lazerduck/fuse-vault/v1/docs/security-design.md

# Fuse Vault security and provisioning design

Review update (2026-09-14): the [storage and responsiveness redesign](storage-performance-redesign.md)
retains Ascon and selectable encryption while proposing a new data layout and
measured password-hardening budget. Existing recovery and KDF descriptions below
describe the prototype; the redesign remains a review draft, not implemented code.

Status: architectural baseline for development. Cryptographic profile details
remain provisional until they have test vectors, measurements on RP2354A, and
independent review.

## Security objective

Fuse Vault provides encrypted storage at rest and deliberate, selective
disclosure after local user authentication. The host never receives the vault
unlock secret, device secret, volume master key, or derived storage keys. A
host can access plaintext that the user deliberately exposes while the relevant
USB mode is active; the device cannot protect that plaintext from a malicious
host after disclosure.

The design does not depend on a single cryptographic family. During V1 setup the
user selects an ordered stack from algorithms compiled into the reviewed
firmware registry. Vault-header format V2 authenticates one to four permanent
algorithm IDs and versions. This is not arbitrary user-supplied code: unknown or
unavailable algorithms fail locked and are never silently replaced.

## Key hierarchy

The following values have distinct roles:

- **Entry encoding:** canonical, versioned bytes generated by the selected
  human-input method. It is not a cryptographic key.
- **Input key:** a 32-byte result from a password-hardening function using the
  entry encoding, a random per-vault salt, and stored parameters.
- **Device roots:** two independently generated random 32-byte values unique
  to the physical device. Neither is ever stored on the SD card. The roots are
  assigned permanently to the SHA-256 and Keccak families and are never used
  directly as operational keys.
- **Key-encryption keys:** independent values derived from the input key and
  corresponding device root by the profile's two cryptographic families.
- **Volume master key (VMK):** a random 32-byte value generated during setup.
  It is wrapped by both profile branches and is never derived directly from
  human input.
- **Layer keys:** keys derived from the VMK with unique labels containing the
  profile version, algorithm identifier, direction/purpose, and vault ID.

Changing an entry method or secret rewraps the random VMK after successful
authentication; it does not require re-encrypting every data block.

The implemented selectable data layers are AES-256-XTS and ChaCha20. Their
ordered transforms sit inside the mandatory Ascon-AEAD128 storage record, which
provides authenticated addressing, metadata integrity, and torn-write recovery.
SM4-XTS has a reserved identifier but is unavailable rather than a no-op.

## Default dual-family profile

The implemented provisional V1 profile uses two independently designed
derivation and wrapping branches, both of which are required to unlock the
VMK:

1. PBKDF2-HMAC-SHA-256 hardens the canonical entry with a random salt and a
   recorded iteration count. HMAC-SHA-256 then combines that result with device
   Root A to derive an AES-256-GCM key. AES-256-GCM forms the inner envelope.
2. A versioned iterated-KMAC256 construction hardens the same canonical entry
   under an independent salt, iteration count, and encoding. KMAC256 combines
   that result with Root B to derive a 128-bit Ascon key. NIST Ascon-AEAD128
   authenticates the complete inner envelope as the outer layer.

The fixed envelope is 92 bytes: a 16-byte Ascon nonce, a 60-byte encrypted
inner envelope, and a 16-byte Ascon tag. The inner envelope contains a 12-byte
AES nonce, 32-byte encrypted VMK, and 16-byte AES-GCM tag. Both AEAD layers use
the same canonical associated data containing the envelope version, header
sequence, profile ID, entry-method ID, vault ID, both salts, both costs, and
wrapped length. A wrong entry, either wrong device root, or alteration of any
authenticated metadata therefore prevents VMK recovery.

PBKDF2 was selected for the first implementation instead of committing to
scrypt parameters before RP2354A SRAM use and latency can be measured. The
device-held roots and rollback-resistant ten-attempt limit prevent an SD-card
image from becoming a standalone password oracle, but the final iteration
counts and whether the SHA branch moves to scrypt remain review items. Header
costs are bounded to prevent malicious metadata from causing unbounded work.

Every cryptographic operation has a fixed ASCII domain label beginning with
`fuse-vault/v1/`. All variable-length inputs use length-prefix encoding. The
profile ID and all parameters required to reproduce derivation are
authenticated metadata.

The primary references are [NIST SP 800-132 for
PBKDF2](https://csrc.nist.gov/pubs/sp/800/132/final), [NIST SP 800-185 for
KMAC](https://csrc.nist.gov/pubs/sp/800/185/final), [NIST SP 800-38D for
GCM](https://csrc.nist.gov/pubs/sp/800/38/d/final), and [NIST SP 800-232 for
Ascon](https://csrc.nist.gov/pubs/sp/800/232/final). Reference documents do not
by themselves constitute a review of the composed Fuse Vault profile.

## Vault header

The removable card contains redundant authenticated copies of a versioned
header. At minimum it records:

- format version and header sequence number;
- random vault ID;
- crypto profile ID;
- entry-method ID and encoding version;
- salts and KDF parameters for both branches;
- ordered data-encryption layer identifiers and parameters;
- the twice-wrapped VMK and its authentication data;
- encrypted filesystem geometry and integrity-tree roots where applicable.

The header contains no device secret and no independent verifier of the human
secret. Correct authentication is established only by successfully validating
both wrapping layers and the authenticated header.

## First-time setup

An unprovisioned device exposes no USB data interface. The setup sequence is:

1. Explain that no vault exists and require an explicit start action.
2. Run hardware and entropy-source checks.
3. Select an entry method and its versioned configuration.
4. Enter the secret twice and compare canonical encodings.
5. Confirm the ten-attempt destructive-lockout and no-recovery policy.
6. Generate the device secret, vault ID, salts, and VMK from the approved random
   source.
7. Calibrate or select the fixed, recorded profile parameters.
8. Derive both wrapping keys and wrap the VMK through both profile branches.
9. Initialise the encrypted card and redundant authenticated headers.
10. Persist rollback-resistant attempt state at zero.
11. Erase transient inputs and derived keys from RAM.
12. Require a complete verification unlock before marking setup complete.

The implemented `device_provisioning.c` transaction covers the device-root and
initial-journal portion of this sequence. Its critical commit order is journal
erase, authenticated initial-record write, journal verification, OTP root
write, OTP active-marker write, root read-back, and a second journal
verification using the read-back roots. It is intentionally not connected to
the setup-success event until the KDF, wrapped VMK, and vault-header stages can
run before the OTP active marker.

OTP and permanent secure-boot settings are not changed by ordinary development
firmware. Production OTP provisioning is a separate, deliberately invoked
process with read-back verification before irreversible lock bits are set.
The proposed device-secret lifecycle and RP2354A storage mapping are detailed in
[rp2354-storage.md](rp2354-storage.md).

## Attempt accounting

An attempt must be durably reserved before an entered secret is checked. This
prevents power removal during authentication from providing unlimited free
guesses. Successful authentication resets the counter only after both wrapping
layers and the authenticated header validate.

The application state machine enforces this ordering by entering an
attempt-reservation state and emitting only a persistent-counter command. It
cannot emit the authentication command until the platform acknowledges that
write. The host development backend implements this with two alternating,
sequence-numbered records and atomic file replacement; its CRC is only for
corruption recovery and is not the production counter-authentication design.

The portable production journal core uses two flash sectors, append-only
256-byte records, sequence linkage, vault binding, and two independent
authentication tags. Recovery ignores torn or unauthenticated records and
sector rotation retains the latest valid record before erasing old history.
The implemented authenticator derives one journal key from Root A using
SP 800-108 counter mode with HMAC-SHA-256 and another from Root B using the
SP 800-108 KMAC256 construction. Full 32-byte HMAC-SHA-256 and KMAC256 tags are
required. Labels and device context separate these keys from every other use.
Host known-answer tests cover the HMAC derivation/tag path and the official
NIST KMAC256 sample. The journal fault-injection tests retain a deliberately
non-cryptographic authenticator so every write boundary can be controlled.

The counter cannot rely solely on the removable card because an attacker could
restore an older card image. Internal-flash journalling prevents ordinary SD
rollback and handles interrupted writes, but an invasive attacker who can clone
and restore the RP2354A's internal flash remains outside this V1 mechanism. The
hardware flash adapter, endurance budget, dual-family MAC implementation, and
behaviour at the tenth reserved attempt remain required before destructive
lockout is enabled on hardware.

## Secret lifecycle

Entry state, canonical encodings, KDF work areas, wrapping keys, the VMK, and
layer keys are separate buffers with explicit owners and lifetimes. Sensitive
buffers are erased on cancellation, failure, mode exit, USB disconnect, and
fault entry. Compiler-resistant erasure and tests of those transitions are
required. The host simulator never implements a plaintext storage fallback.

## Decisions still requiring review

- Final parameters and measured latency for both password-hardening branches,
  including whether scrypt fits the SHA branch on the production board.
- Independent review of the two-family credential-envelope composition.
- Authenticated-encryption algorithms for storage sectors.
- Nonce construction and power-loss-safe authenticated metadata updates.
- Rollback-resistant attempt accounting within flash/OTP endurance limits.
- Secure boot, debug lockdown, firmware update, and recovery policy.
- Side-channel behaviour and constant-time implementation of secret operations.
