lazerduck/fuse-vault/CaseDesign/drill_schedule.csv

x | y | end_x | end_y | diameter | kind | plating | sources
62.52489 | -16.93189 | 62.52489 | -16.93189 | 0.95001 | round | NPTH | Drill_NPTH_Through.DRL:17
58.12511 | -16.93189 | 58.12511 | -16.93189 | 0.95001 | round | NPTH | Drill_NPTH_Through.DRL:18
71.025 | -8.79907 | 71.025 | -8.79907 | 1.0 | round | NPTH | Drill_NPTH_Through.DRL:20
71.025 | -13.29919 | 71.025 | -13.29919 | 1.0 | round | NPTH | Drill_NPTH_Through.DRL:21
52.45405 | -4.07899 | 52.45405 | -4.07899 | 1.2 | round | NPTH | Drill_NPTH_Through.DRL:23
60.45403 | -4.07899 | 60.45403 | -4.07899 | 1.2 | round | NPTH | Drill_NPTH_Through.DRL:24
31.8135 | -1.0795 | 31.8135 | -1.0795 | 0.305 | round | PTH | Drill_PTH_Through.DRL:21;Drill_PTH_Through_Via.DRL:15
31.877 | -2.286 | 31.877 | -2.286 | 0.305 | round | PTH | Drill_PTH_Through.DRL:22;Drill_PTH_Through_Via.DRL:16
42.57501 | -12.51718 | 42.57501 | -12.51718 | 0.305 | round | PTH | Drill_PTH_Through.DRL:24;Drill_PTH_Through_Via.DRL:18
45.07771 | -5.79899 | 45.07771 | -5.79899 | 0.305 | round | PTH | Drill_PTH_Through.DRL:25;Drill_PTH_Through_Via.DRL:19
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
