lazerduck/fuse-vault/CaseDesign/prototype-e/base.step

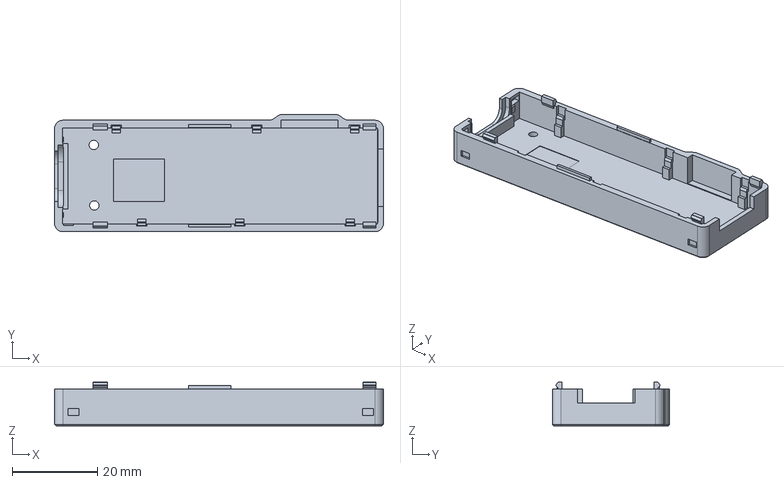
[picture p19: CAD file, 2026-10-05]
CaseDesign/prototype-e/base.step
77.3 x 27.6 x 10.3 mm
