lazerduck/fuse-vault/CaseDesign/prototype-e/lid_snap_light.step

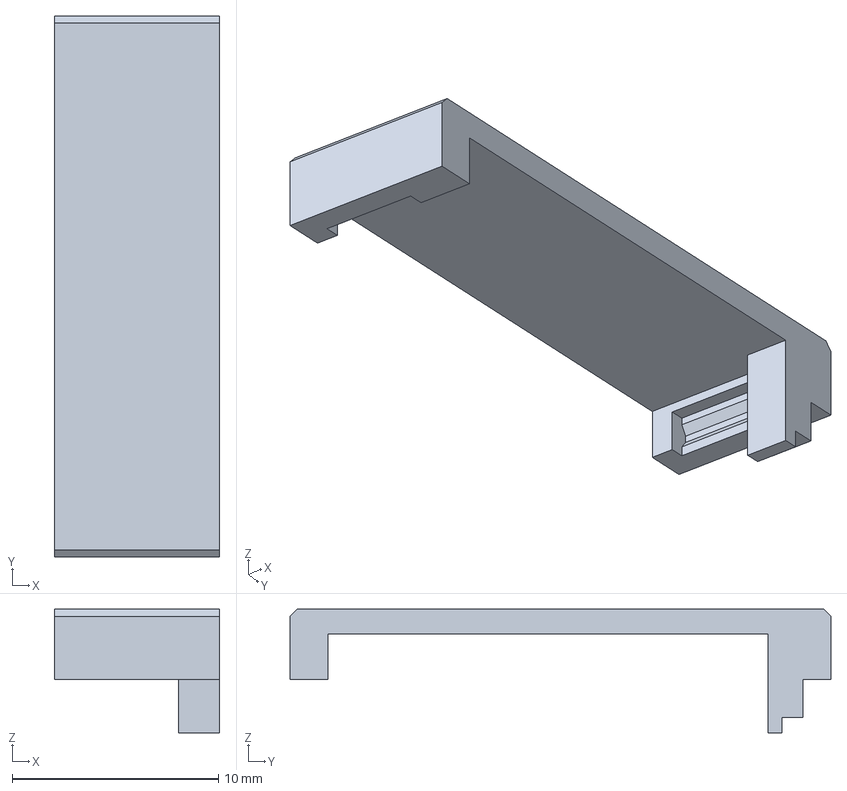
[picture p20: CAD file, 2026-10-05]
CaseDesign/prototype-e/lid_snap_light.step
8.00 x 26.2 x 6.00 mm
