lazerduck/fuse-vault/results/ui-polish-20260921.png

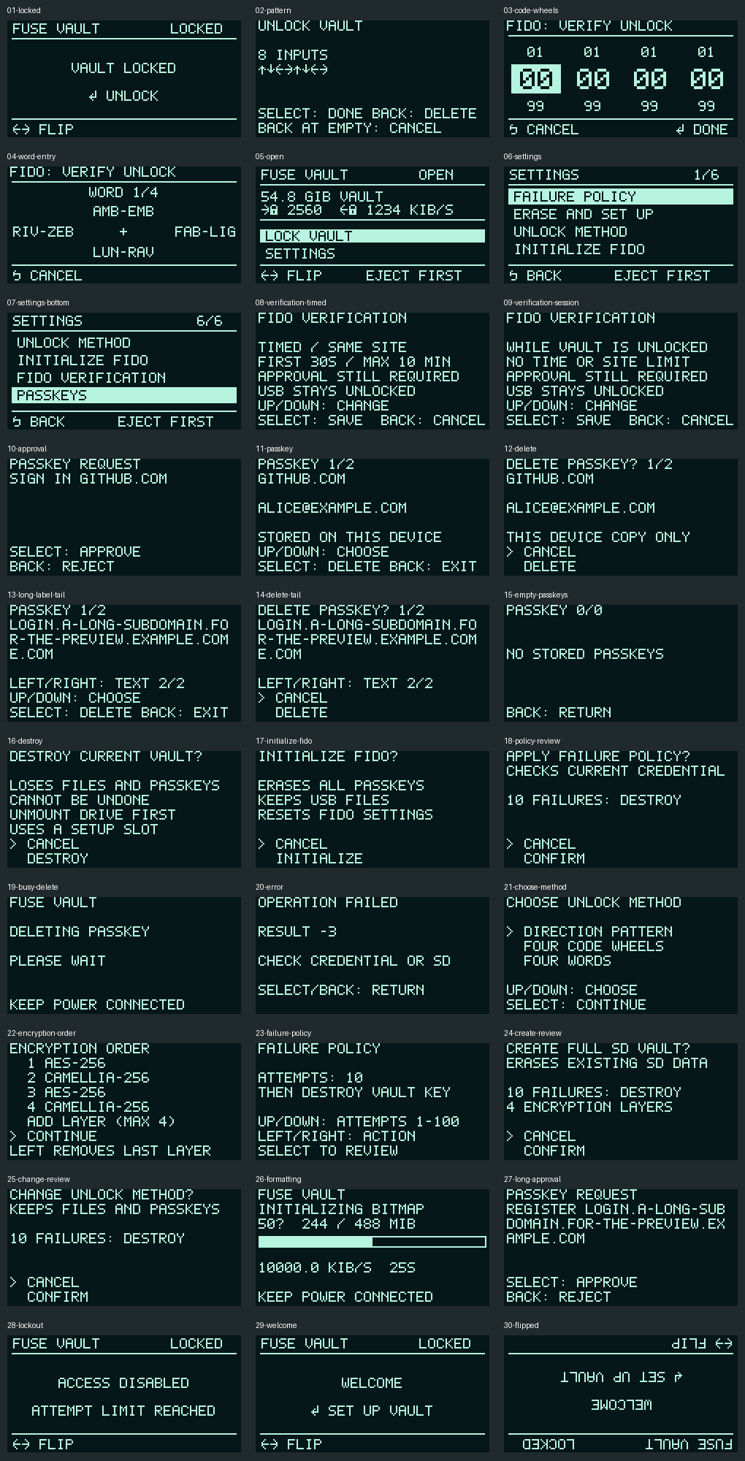
results/ui-polish-20260921.png
