lazerduck/fuse-vault/results/ui-polish-20261001/dashboard.png

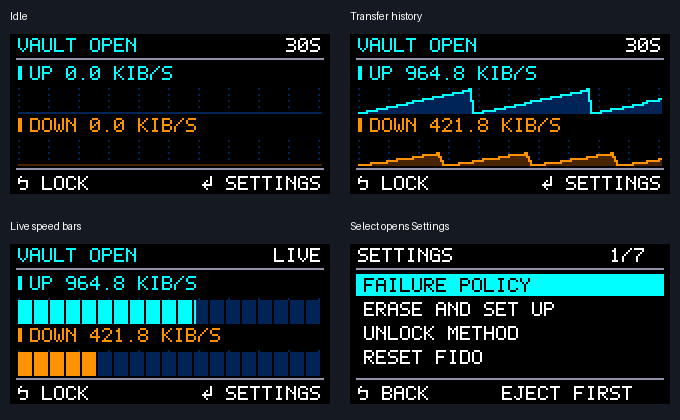
results/ui-polish-20261001/dashboard.png
