lazerduck/fuse-vault/results/ui-polish-20261001/refinements.png

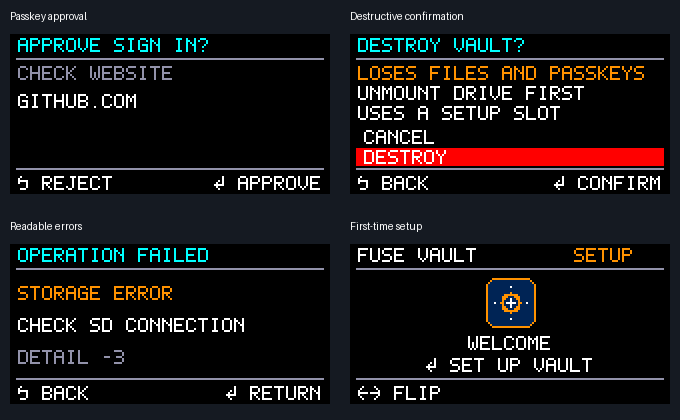
results/ui-polish-20261001/refinements.png
