lazerduck/fuse-vault/results/ui-polish-20261001/screens.png

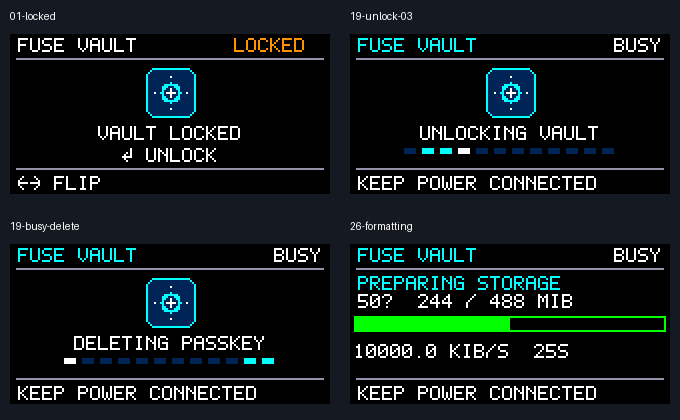
results/ui-polish-20261001/screens.png
