lazerduck/fuse-vault/results/ui-polish-20261001/unlock.gif

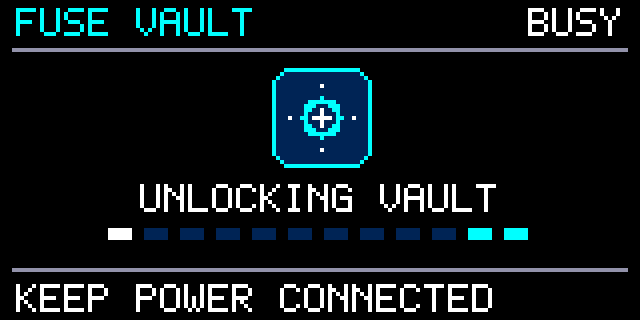
results/ui-polish-20261001/unlock.gif
