lazerduck/fuse-vault/results/ui-style-20260921.png

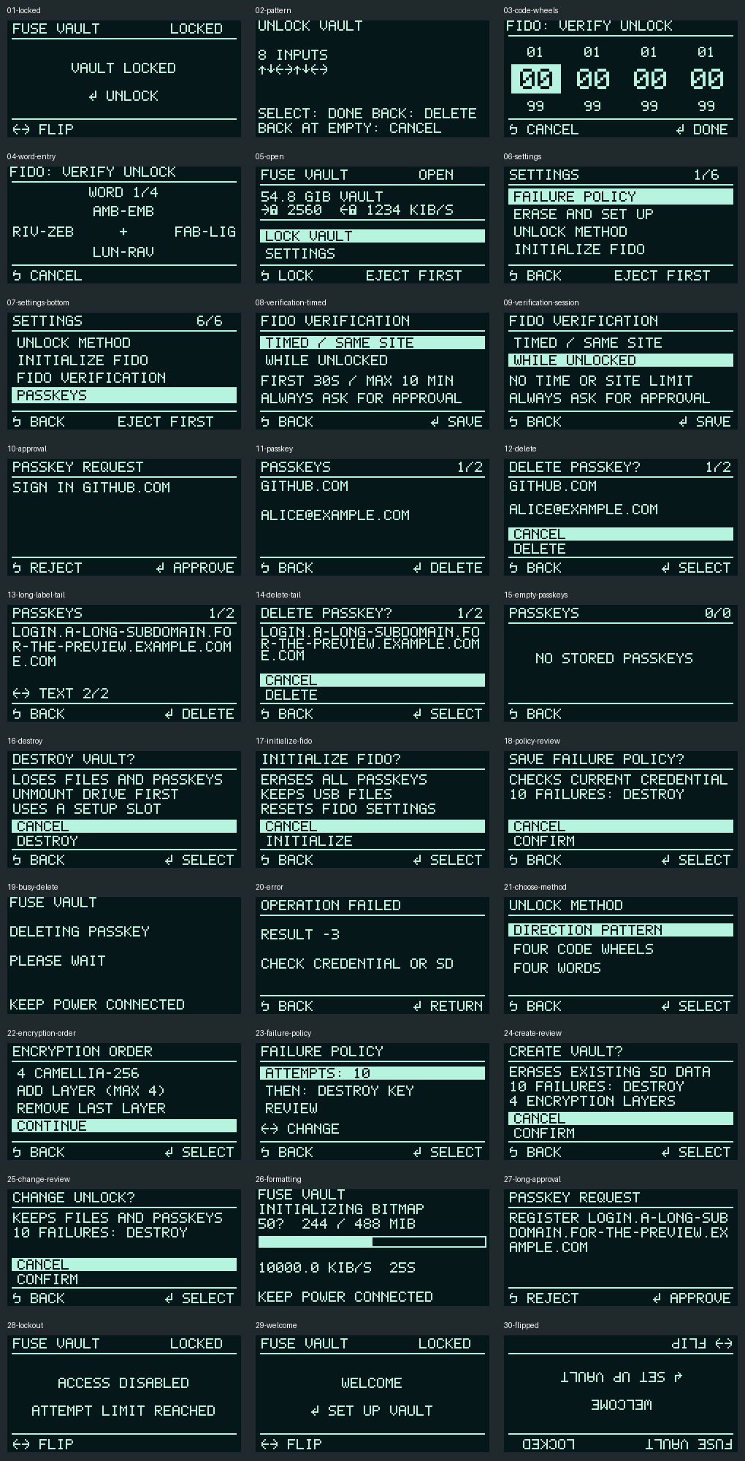
results/ui-style-20260921.png
