lazerduck/fuse-vault/v1/firmware/include/fuse_vault/app.h

#ifndef FUSE_VAULT_APP_H
#define FUSE_VAULT_APP_H

#include "fuse_vault/entry_method.h"
#include "fuse_vault/passkeys.h"
#include "fuse_vault/persistence.h"

#include <stdbool.h>
#include <stdint.h>

#define FV_MAX_UNLOCK_ATTEMPTS 10u
#define FV_UI_LINE_COUNT 4u
#define FV_UI_TEXT_CAPACITY 32u
#define FV_SECRET_WHEEL_COUNT 3u
#define FV_SECRET_WHEEL_VALUES 100u
#define FV_SECRET_DIRECTION_MAX 16u
#define FV_SECRET_KEYPAD_MAX 12u
#define FV_SECRET_WORD_COUNT 4u
#define FV_SECRET_WORD_EMPTY UINT8_MAX

typedef enum {
    FV_STATE_BOOTING = 0,
    FV_STATE_BOOT_MEDIA_REQUIRED,
    FV_STATE_SETUP_REQUIRED,
    FV_STATE_SETUP_MEDIA_CHECKING,
    FV_STATE_SETUP_MEDIA_CONFIRM,
    FV_STATE_SETUP_MEDIA_INITIALIZING,
    FV_STATE_SETUP_MEDIA_ERROR,
    FV_STATE_SETUP_METHOD_SELECT,
    FV_STATE_SETUP_SECRET_ENTRY,
    FV_STATE_SETUP_SECRET_CONFIRM,
    FV_STATE_SETUP_SECRET_MISMATCH,
    FV_STATE_SETUP_STACK_SELECT,
    FV_STATE_SETUP_POLICY_CONFIRM,
    FV_STATE_PROVISIONING,
    FV_STATE_MODE_SELECT,
    FV_STATE_VAULT_SECRET_ENTRY,
    FV_STATE_VAULT_RESERVING_ATTEMPT,
    FV_STATE_VAULT_AUTHENTICATING,
    FV_STATE_VAULT_RECORDING_SUCCESS,
    FV_STATE_VAULT_UNLOCKED,
    FV_STATE_FIDO_READY,
    FV_STATE_PASSKEY_LIST,
    FV_STATE_PASSKEY_DELETE_CONFIRM,
    FV_STATE_SETTINGS,
    FV_STATE_CHANGE_METHOD,
    FV_STATE_CHANGE_SECRET,
    FV_STATE_CHANGE_CONFIRM,
    FV_STATE_CHANGE_MISMATCH,
    FV_STATE_CHANGE_REVIEW,
    FV_STATE_CHANGE_SAVING,
    FV_STATE_CHANGE_SAVED,
    FV_STATE_DESTROYED,
    FV_STATE_FAULT,
} fv_state_t;

typedef enum {
    FV_MODE_VAULT = 0,
    FV_MODE_FIDO,
    FV_MODE_SETTINGS,
    FV_MODE_COUNT,
} fv_mode_t;

typedef enum {
    FV_EVENT_BOOT_COMPLETED = 0,
    FV_EVENT_BOOT_MEDIA_REQUIRED,
    FV_EVENT_UP,
    FV_EVENT_DOWN,
    FV_EVENT_LEFT,
    FV_EVENT_RIGHT,
    FV_EVENT_SELECT,
    FV_EVENT_BACK,
    FV_EVENT_AUTH_SUCCEEDED,
    FV_EVENT_AUTH_FAILED,
    FV_EVENT_ATTEMPT_COUNTER_STORED,
    FV_EVENT_PROVISIONING_SUCCEEDED,
    FV_EVENT_PROVISIONING_FAILED,
    FV_EVENT_MEDIA_FOUND,
    FV_EVENT_MEDIA_PREPARED,
    FV_EVENT_MEDIA_FAILED,
    FV_EVENT_LOCK_REQUESTED,
    FV_EVENT_USB_EJECTED,
    FV_EVENT_STORAGE_FAILED,
    FV_EVENT_CREDENTIAL_CHANGED,
    FV_EVENT_FATAL_ERROR,
} fv_event_t;

typedef enum {
    FV_COMMAND_NONE = 0,
    FV_COMMAND_BEGIN_PROVISIONING = 1u << 0,
    FV_COMMAND_BEGIN_AUTHENTICATION = 1u << 1,
    FV_COMMAND_USB_ATTACH_MSC = 1u << 2,
    FV_COMMAND_USB_ATTACH_FIDO = 1u << 3,
    FV_COMMAND_USB_DETACH = 1u << 4,
    FV_COMMAND_ERASE_TRANSIENT_SECRET = 1u << 5,
    FV_COMMAND_ERASE_SESSION_KEYS = 1u << 6,
    FV_COMMAND_DESTROY_DEVICE_SECRET = 1u << 7,
    FV_COMMAND_STORE_ATTEMPT_COUNTER = 1u << 8,
    FV_COMMAND_INSPECT_MEDIA = 1u << 9,
    FV_COMMAND_PREPARE_MEDIA = 1u << 10,
    FV_COMMAND_PASSKEY_BEGIN = 1u << 11,
    FV_COMMAND_PASSKEY_READ = 1u << 12,
    FV_COMMAND_PASSKEY_DELETE = 1u << 13,
    FV_COMMAND_PASSKEY_END = 1u << 14,
    FV_COMMAND_CHANGE_CREDENTIAL = 1u << 15,
} fv_command_t;

typedef uint32_t fv_command_set_t;

typedef struct {
    uint8_t values[FV_SECRET_WHEEL_COUNT];
    uint8_t selected;
} fv_wheel_entry_t;

typedef struct {
    uint8_t values[FV_SECRET_DIRECTION_MAX];
    uint8_t length;
} fv_direction_entry_t;

typedef struct {
    uint8_t digits[FV_SECRET_KEYPAD_MAX];
    uint8_t length;
    uint8_t selected;
} fv_keypad_entry_t;

typedef struct {
    uint8_t words[FV_SECRET_WORD_COUNT];
    uint8_t selected;
    uint8_t depth; /* Number of four-way groups chosen: 0, 1, or 2. */
    uint8_t prefix;
    bool reviewing;
} fv_word_entry_t;

typedef struct {
    fv_entry_method_t method;
    union {
        fv_wheel_entry_t wheels;
        fv_direction_entry_t directions;
        fv_keypad_entry_t keypad;
        fv_word_entry_t word_list;
    } state;
} fv_secret_entry_t;

typedef struct {
    fv_state_t state;
    fv_mode_t selected_mode;
    fv_entry_method_t selected_entry_method;
    fv_secret_entry_t secret_entry;
    fv_secret_entry_t setup_secret_entry;
    /* Settings draft never replaces the active method until durable commit. */
    fv_secret_entry_t change_secret_entry;
    fv_entry_method_t change_entry_method;
    uint8_t selected_setting;
    fv_encryption_stack_descriptor_t selected_encryption_stack;
    uint8_t selected_stack_preset;
    uint8_t failed_attempts;
    bool provisioned;
    bool fido_available;
    bool session_unlocked;
    bool fido_waiting;
    bool fido_reset_pending;
    fv_passkey_t passkey;
    uint16_t passkey_index, passkey_count, passkey_offset;
} fv_app_t;

typedef struct {
    bool secret_controls;
    bool hide_controls;
    bool direction_icons;
    bool word_picker;
    char word_choices[4][12]; /* Up, Right, Down, Left. */
    bool select_enabled;
    char back_action[8];
    char select_action[8];
    char title[FV_UI_TEXT_CAPACITY];
    char lines[FV_UI_LINE_COUNT][FV_UI_TEXT_CAPACITY];
} fv_ui_view_t;

void fv_app_init(fv_app_t *app, bool provisioned, uint8_t persisted_failed_attempts,
                 fv_entry_method_t entry_method);
void fv_app_set_fido_available(fv_app_t *app, bool available);
fv_command_set_t fv_app_handle(fv_app_t *app, fv_event_t event);
void fv_app_render(const fv_app_t *app, fv_ui_view_t *view);
const char *fv_state_name(fv_state_t state);

#endif
