lazerduck/fuse-vault/v1/firmware/src/rp2354_usb_descriptors.c

#include "pico/unique_id.h"
#include "tusb.h"
#include "fuse_vault/rp2354_usb_msc.h"

#include <stddef.h>
#include <stdint.h>
#include <string.h>

#ifndef FUSE_VAULT_USB_VID
/* TinyUSB development VID. A production-assigned VID/PID is a release gate. */
#define FUSE_VAULT_USB_VID 0xcafeu
#endif
#ifndef FUSE_VAULT_USB_PID
#if FUSE_VAULT_HEADLESS_DEBUG
#define FUSE_VAULT_USB_PID 0x4013u
#else
#define FUSE_VAULT_USB_PID 0x4011u
#endif
#endif

static const tusb_desc_device_t DEVICE = {
    .bLength = sizeof(tusb_desc_device_t),
    .bDescriptorType = TUSB_DESC_DEVICE,
    .bcdUSB = 0x0200,
#if FUSE_VAULT_HEADLESS_DEBUG
    .bDeviceClass = TUSB_CLASS_MISC,
    .bDeviceSubClass = MISC_SUBCLASS_COMMON,
    .bDeviceProtocol = MISC_PROTOCOL_IAD,
#else
    .bDeviceClass = 0x00,
    .bDeviceSubClass = 0x00,
    .bDeviceProtocol = 0x00,
#endif
    .bMaxPacketSize0 = CFG_TUD_ENDPOINT0_SIZE,
    .idVendor = FUSE_VAULT_USB_VID,
    .idProduct = FUSE_VAULT_USB_PID,
    .bcdDevice = 0x0100,
    .iManufacturer = 1,
    .iProduct = 2,
    .iSerialNumber = 3,
    .bNumConfigurations = 1,
};

uint8_t const *tud_descriptor_device_cb(void) {
#if FUSE_VAULT_ENABLE_FIDO2
    /* Distinct development PID avoids cached MSC descriptors in HID mode.
     * The prototype cannot be enabled in production builds. */
    static tusb_desc_device_t fido_device;
    if (fv_rp2354_usb_is_fido()) {
        fido_device = DEVICE;
        fido_device.idProduct = 0x4012u;
        return (const uint8_t *)&fido_device;
    }
#endif
    return (const uint8_t *)&DEVICE;
}

#if FUSE_VAULT_HEADLESS_DEBUG
enum { INTERFACE_MSC, INTERFACE_CDC, INTERFACE_CDC_DATA, INTERFACE_COUNT };
#define CONFIG_LENGTH (TUD_CONFIG_DESC_LEN + TUD_MSC_DESC_LEN + TUD_CDC_DESC_LEN)
#else
enum { INTERFACE_MSC, INTERFACE_COUNT };
#define CONFIG_LENGTH (TUD_CONFIG_DESC_LEN + TUD_MSC_DESC_LEN)
#endif
static const uint8_t CONFIGURATION[] = {
    TUD_CONFIG_DESCRIPTOR(1, INTERFACE_COUNT, 0, CONFIG_LENGTH,
                          TUSB_DESC_CONFIG_ATT_REMOTE_WAKEUP, 100),
    TUD_MSC_DESCRIPTOR(INTERFACE_MSC, 0, 0x01, 0x81, 64),
#if FUSE_VAULT_HEADLESS_DEBUG
    TUD_CDC_DESCRIPTOR(INTERFACE_CDC, 0, 0x82, 8, 0x03, 0x83, 64),
#endif
};

#if FUSE_VAULT_ENABLE_FIDO2
static const uint8_t FIDO_REPORT[] = { TUD_HID_REPORT_DESC_FIDO_U2F(64) };
static const uint8_t FIDO_CONFIGURATION[] = {
    TUD_CONFIG_DESCRIPTOR(1, 1, 0, TUD_CONFIG_DESC_LEN + TUD_HID_INOUT_DESC_LEN, 0, 100),
    TUD_HID_INOUT_DESCRIPTOR(0, 0, HID_ITF_PROTOCOL_NONE, sizeof(FIDO_REPORT),
                            0x01, 0x81, 64, 5),
};
uint8_t const *tud_hid_descriptor_report_cb(uint8_t instance) {
    return instance == 0 && fv_rp2354_usb_is_fido() ? FIDO_REPORT : NULL;
}
#endif

uint8_t const *tud_descriptor_configuration_cb(uint8_t index) {
    (void)index;
#if FUSE_VAULT_ENABLE_FIDO2
    if (fv_rp2354_usb_is_fido()) return FIDO_CONFIGURATION;
#endif
    return CONFIGURATION;
}

static uint16_t string_buffer[33];

uint16_t const *tud_descriptor_string_cb(uint8_t index, uint16_t language_id) {
    (void)language_id;
    const char *ascii = NULL;
    char serial[2u * PICO_UNIQUE_BOARD_ID_SIZE_BYTES + 1u];
    size_t length = 0u;
    if (index == 0u) {
        string_buffer[1] = 0x0409u;
        length = 1u;
    } else {
        if (index == 1u) ascii = "Fuse Vault";
        else if (index == 2u) ascii =
#if defined(FUSE_VAULT_USB_PRODUCT)
            FUSE_VAULT_USB_PRODUCT;
#elif FUSE_VAULT_HEADLESS_DEBUG
            "Fuse Vault SCREEN DEBUG";
#else
            fv_rp2354_usb_is_fido()
            ? "Fuse Vault FIDO Probe" : "Encrypted Storage";
#endif
        else if (index == 3u) {
            pico_get_unique_board_id_string(serial, sizeof(serial));
            ascii = serial;
        } else return NULL;
        length = strlen(ascii);
        if (length > 32u) length = 32u;
        for (size_t character = 0u; character < length; ++character) {
            string_buffer[character + 1u] = (uint16_t)(uint8_t)ascii[character];
        }
    }
    string_buffer[0] = (uint16_t)((TUSB_DESC_STRING << 8u) |
                                  (uint16_t)(2u * length + 2u));
    return string_buffer;
}
