lazerduck/fuse-vault/v1/firmware/include/fuse_vault/fido_engine.h

#ifndef FUSE_VAULT_FIDO_ENGINE_H
#define FUSE_VAULT_FIDO_ENGINE_H
#include "fuse_vault/passkeys.h"
#include <stdbool.h>
#include <stddef.h>
#include <stdint.h>
#define FV_FIDO_STORE_BYTES 65536u
#define FV_FIDO_ENGINE_MESSAGE_SIZE 2048u
/* One synchronous engine instance. The platform pumps USB/UI/safety during
 * presence waits; a durable commit must finish before returning success. */
typedef struct {
    bool (*random)(void *, uint8_t *, size_t);
    bool (*commit)(void *, const uint8_t *, size_t);
    int (*presence)(void *); /* 0 approved, 1 timeout, 2 cancelled */
    uint32_t (*millis)(void *);
    /* Optional built-in UV. NULL preserves the external ClientPIN test profile. */
    bool (*verify_user)(void *, const uint8_t *rp_hash);
    uint8_t (*uv_retries)(void *);
    bool (*cancelled)(void *);
    bool (*local_authorized)(void *); /* Device session only; never host UV. */
    void *context;
} fv_fido_engine_ops_t;
bool fv_fido_engine_open(uint8_t store[FV_FIDO_STORE_BYTES],
    const uint8_t root[32], const uint8_t device_id[16],
    const fv_fido_engine_ops_t *ops);
void fv_fido_engine_close(void);
/* Only called by the local UI after unlock. BEGIN blocks host commands until
 * END/close. DELETE requires the stable ID returned by READ and commits before
 * success. A failure requires closing/recovering the engine. */
bool fv_fido_engine_manage(fv_passkey_action_t action, uint16_t *index,
    uint16_t *count, fv_passkey_t *entry);
size_t fv_fido_engine_command(const uint8_t *request, size_t size,
                             uint8_t *response, size_t capacity);
size_t fv_fido_engine_command_channel(uint32_t channel, const uint8_t *request,
    size_t size, uint8_t *response, size_t capacity);
#endif
