lazerduck/fuse-vault/v1/firmware/include/fuse_vault/fido_verification.h

#ifndef FUSE_VAULT_FIDO_VERIFICATION_H
#define FUSE_VAULT_FIDO_VERIFICATION_H
#include <stdbool.h>
#include <stdint.h>
#define FV_FIDO_UV_START_MS 30000u
#define FV_FIDO_UV_COMPLETE_MS 600000u
typedef struct {
    uint32_t verified_at;
    uint8_t rp_hash[32];
    bool valid, started, bound;
} fv_fido_verification_t;
void fv_fido_verification_begin(fv_fido_verification_t *state, uint32_t now);
void fv_fido_verification_clear(fv_fido_verification_t *state);
/* NULL RP is for management operations; later first RP use binds the cache. */
bool fv_fido_verification_use(fv_fido_verification_t *state, uint32_t now,
                               const uint8_t *rp_hash);
#endif
