lazerduck/fuse-vault/v1/firmware/mbedtls_config.h

#ifndef FUSE_VAULT_MBEDTLS_CONFIG_H
#define FUSE_VAULT_MBEDTLS_CONFIG_H

#include <limits.h>

/* Minimal Mbed TLS surface used by the credential envelope. */
#define MBEDTLS_AES_C
#define MBEDTLS_AES_FEWER_TABLES
#define MBEDTLS_CIPHER_MODE_XTS
#define MBEDTLS_CHACHA20_C
#define MBEDTLS_CIPHER_C
#define MBEDTLS_GCM_C

#if FUSE_VAULT_ENABLE_FIDO2
#define MBEDTLS_CHACHAPOLY_C
#define MBEDTLS_POLY1305_C
#define MBEDTLS_ASN1_PARSE_C
#define MBEDTLS_ASN1_WRITE_C
#define MBEDTLS_BASE64_C
#define MBEDTLS_BIGNUM_C
#define MBEDTLS_CIPHER_MODE_CBC
#define MBEDTLS_CIPHER_MODE_CFB
#define MBEDTLS_CIPHER_MODE_CTR
#define MBEDTLS_CIPHER_PADDING_PKCS7
#define MBEDTLS_ECDH_C
#define MBEDTLS_ECDSA_C
#define MBEDTLS_ECP_C
#define MBEDTLS_ECP_DP_SECP256R1_ENABLED
#define MBEDTLS_ECP_DP_SECP384R1_ENABLED
#define MBEDTLS_ECP_DP_SECP521R1_ENABLED
#define MBEDTLS_ECP_DP_SECP256K1_ENABLED
#define MBEDTLS_ECP_DP_CURVE25519_ENABLED
#define MBEDTLS_ECP_DP_CURVE448_ENABLED
#define MBEDTLS_HKDF_C
#define MBEDTLS_MD_C
#define MBEDTLS_OID_C
#define MBEDTLS_PK_C
#define MBEDTLS_PK_PARSE_C
#define MBEDTLS_PK_WRITE_C
#define MBEDTLS_PKCS5_C
#define MBEDTLS_RSA_C
#define MBEDTLS_PKCS1_V15
#define MBEDTLS_PKCS1_V21
#define MBEDTLS_SHA1_C
#define MBEDTLS_SHA224_C
#define MBEDTLS_SHA256_C
#define MBEDTLS_SHA384_C
#define MBEDTLS_SHA512_C
#define MBEDTLS_X509_USE_C
#define MBEDTLS_X509_CREATE_C
#define MBEDTLS_X509_CRT_PARSE_C
#define MBEDTLS_X509_CRT_WRITE_C
#endif

#endif
